B-HS/keyboard/dist/assets/1x1.5 R1-AGZeUWU5.stl

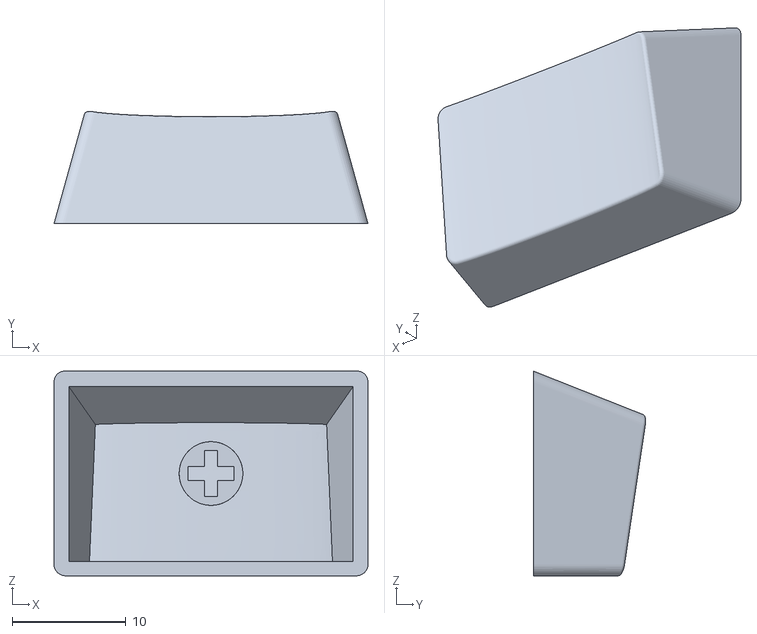
[picture p17: CAD file, 2026-04-19]
dist/assets/1x1.5 R1-AGZeUWU5.stl
27.6 x 9.86 x 18.0
