B-HS/keyboard/dist/assets/1x2 R3-Cc2chU7F.stl

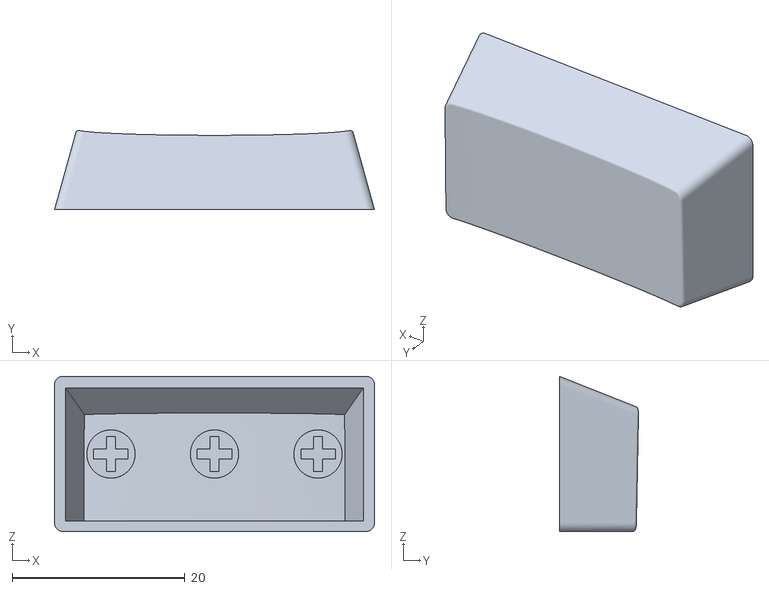
[picture p18: CAD file, 2026-04-19]
dist/assets/1x2 R3-Cc2chU7F.stl
37.1 x 9.17 x 18.0
