B-HS/keyboard/dist/assets/1x2 R2-B7yHtqF7.stl

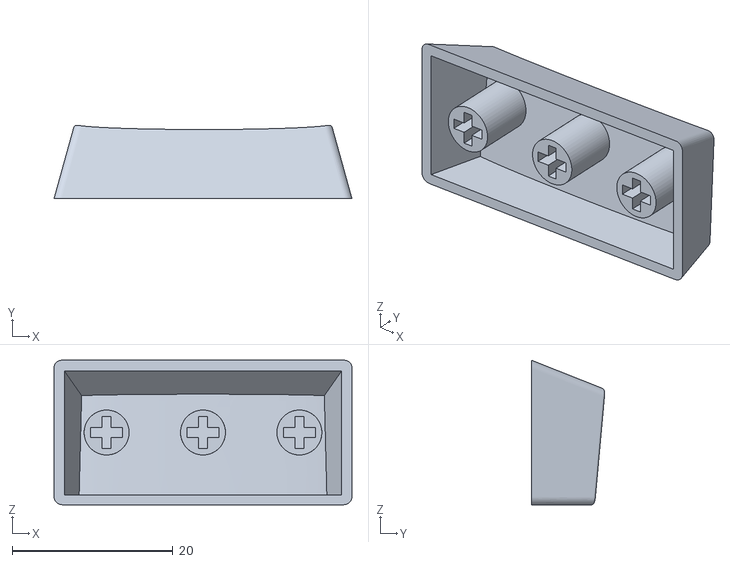
[picture p19: CAD file, 2026-04-19]
dist/assets/1x2 R2-B7yHtqF7.stl
37.1 x 9.12 x 18.0
