B-HS/keyboard/dist/assets/1x1.75 R2-CVJApBdu.stl

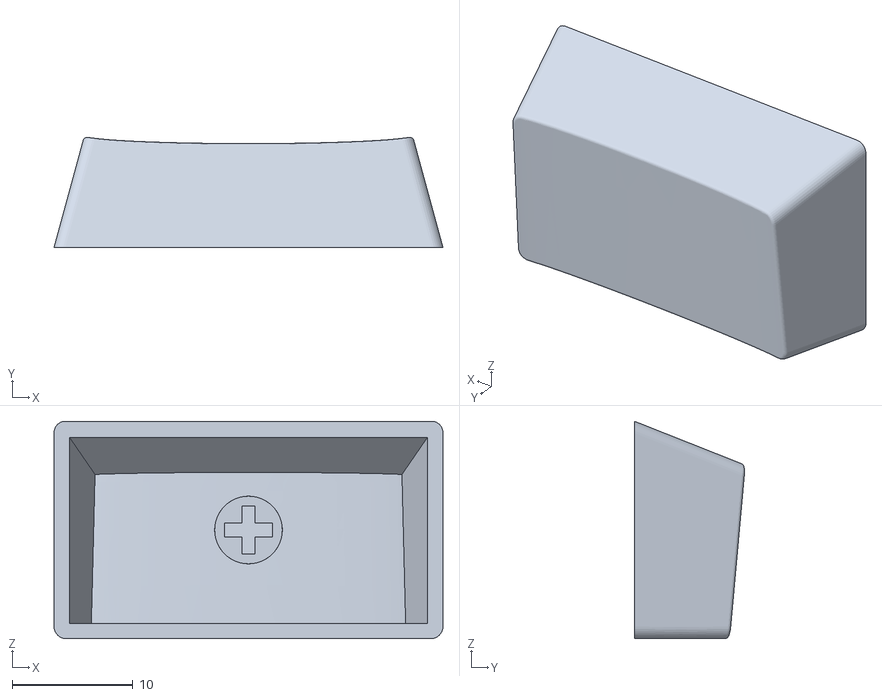
[picture p20: CAD file, 2026-04-19]
dist/assets/1x1.75 R2-CVJApBdu.stl
32.2 x 9.10 x 18.0
