B-HS/keyboard/dist/assets/1x1 R2-BPDmK7m8.stl

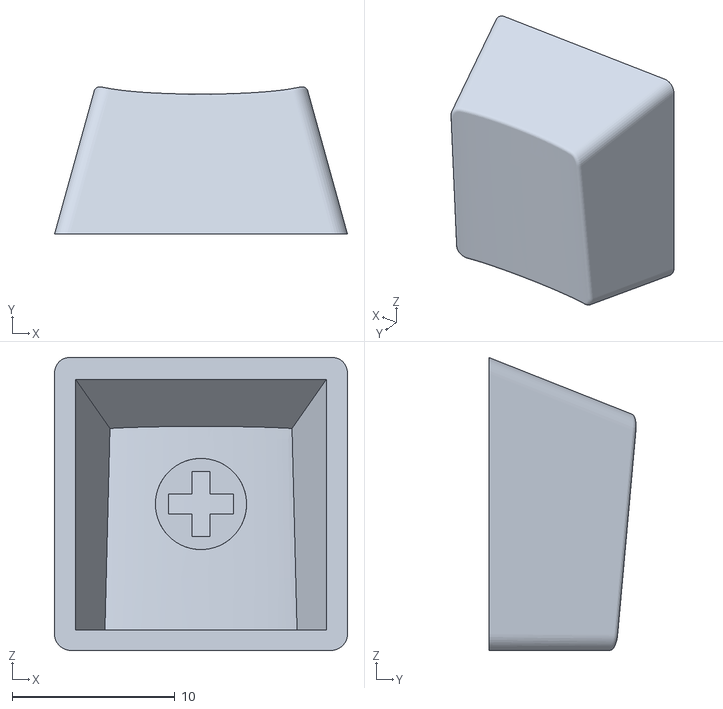
[picture p21: CAD file, 2026-04-19]
dist/assets/1x1 R2-BPDmK7m8.stl
18.0 x 9.04 x 18.0
