B-HS/keyboard/dist/assets/1x1.75 R4-D09ORx_c.stl

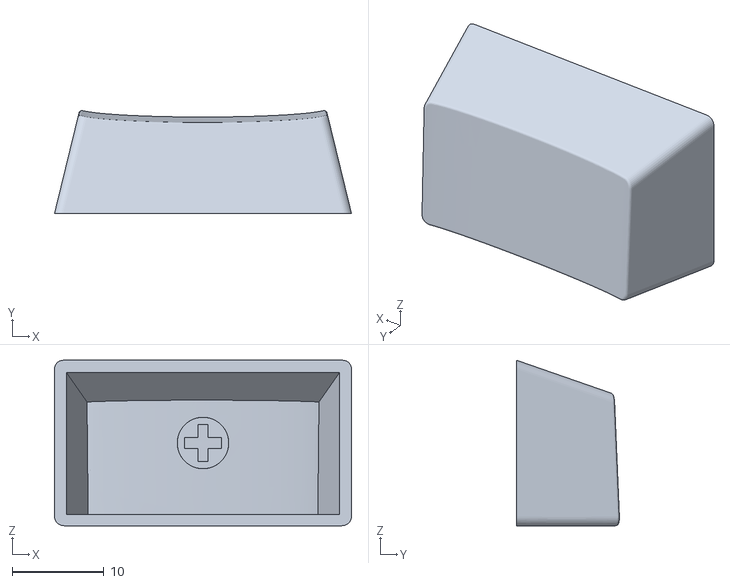
[picture p22: CAD file, 2026-04-19]
dist/assets/1x1.75 R4-D09ORx_c.stl
32.3 x 11.2 x 18.0
