B-HS/keyboard/dist/assets/1x1.75 R1-Bo90p1ow.stl

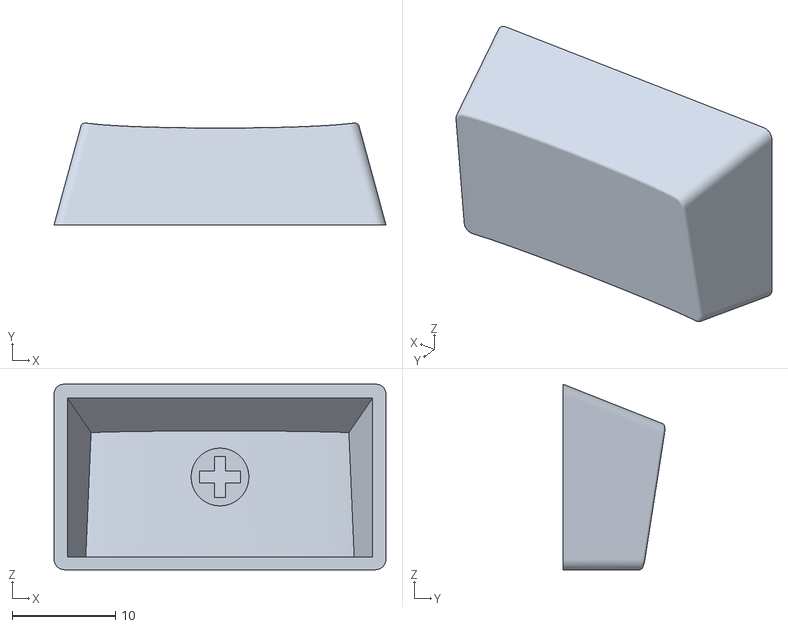
[picture p23: CAD file, 2026-04-19]
dist/assets/1x1.75 R1-Bo90p1ow.stl
32.2 x 9.87 x 18.0
