B-HS/keyboard/dist/assets/1x1.5 R2-BYpHddNk.stl

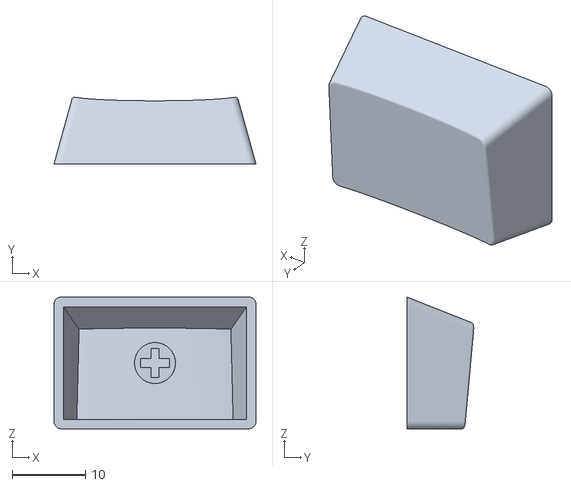
[picture p24: CAD file, 2026-04-19]
dist/assets/1x1.5 R2-BYpHddNk.stl
27.6 x 9.09 x 18.0
