B-HS/keyboard/dist/assets/1x2 R4-B8nouRfq.stl

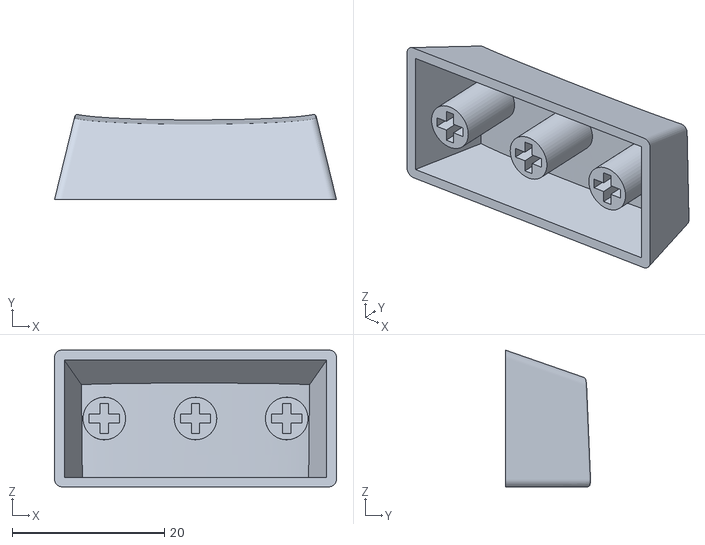
[picture p25: CAD file, 2026-04-19]
dist/assets/1x2 R4-B8nouRfq.stl
37.1 x 11.2 x 18.0
