B-HS/keyboard/dist/assets/1x1.5 R4-Dm8Txsvt.stl

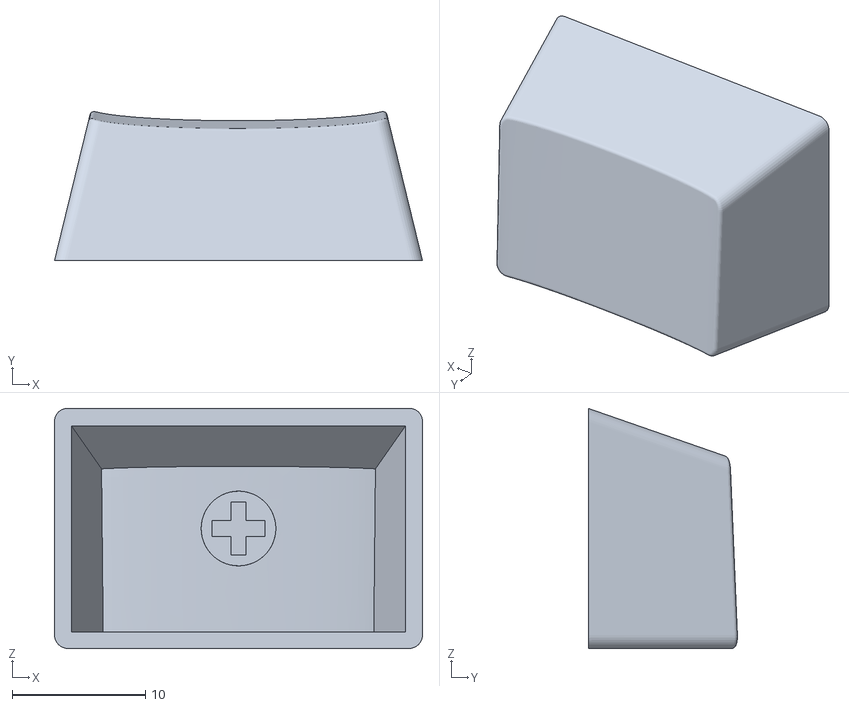
[picture p26: CAD file, 2026-04-19]
dist/assets/1x1.5 R4-Dm8Txsvt.stl
27.6 x 11.2 x 18.0
