B-HS/keyboard/dist/assets/1x1 R3-C7WHg33m.stl

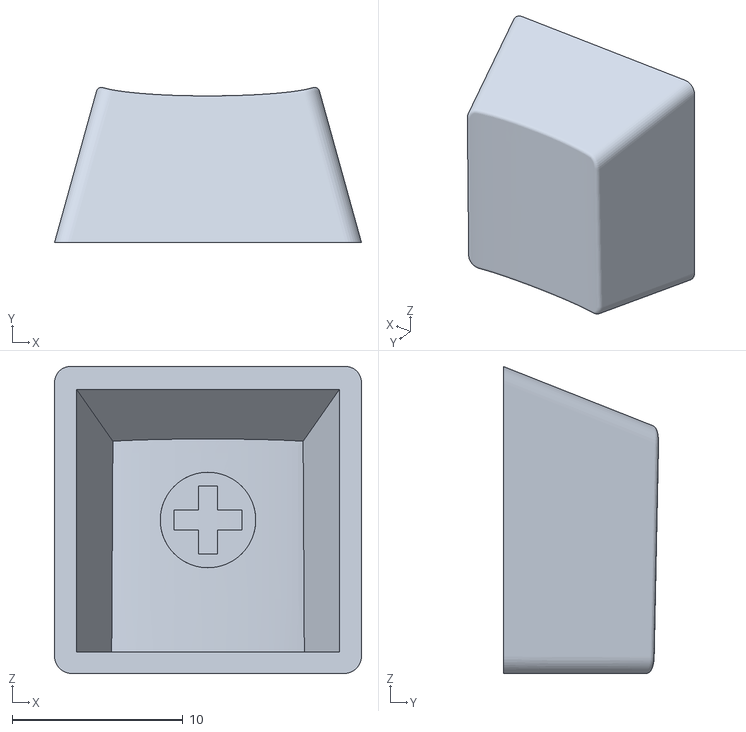
[picture p27: CAD file, 2026-04-19]
dist/assets/1x1 R3-C7WHg33m.stl
18.0 x 9.09 x 18.0
