B-HS/keyboard/dist/assets/1x1 R1-C5EL7BkD.stl

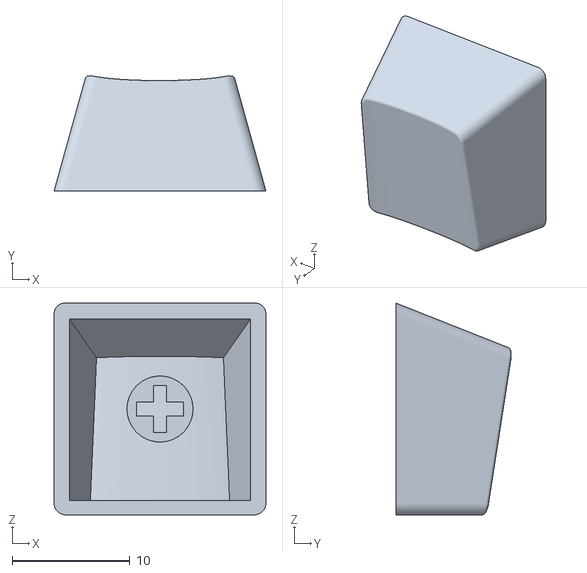
[picture p28: CAD file, 2026-04-19]
dist/assets/1x1 R1-C5EL7BkD.stl
18.0 x 9.80 x 18.0
