B-HS/keyboard/dist/assets/1x2 R1-t59L7Y_R.stl

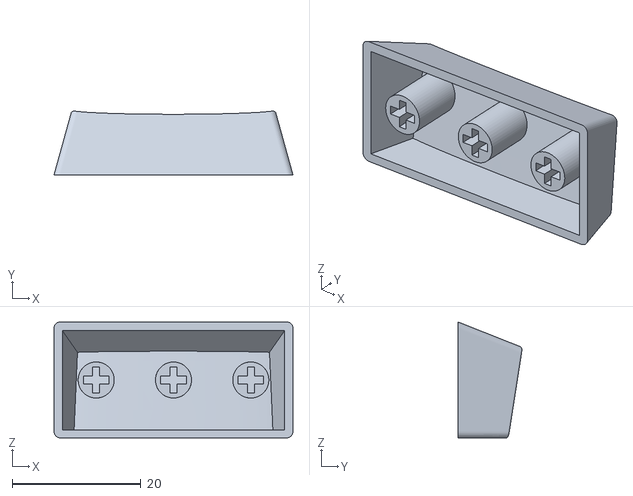
[picture p29: CAD file, 2026-04-19]
dist/assets/1x2 R1-t59L7Y_R.stl
37.1 x 9.88 x 18.0
