B-HS/keyboard/dist/assets/1x2.5 R3-bn9iJfxd.stl

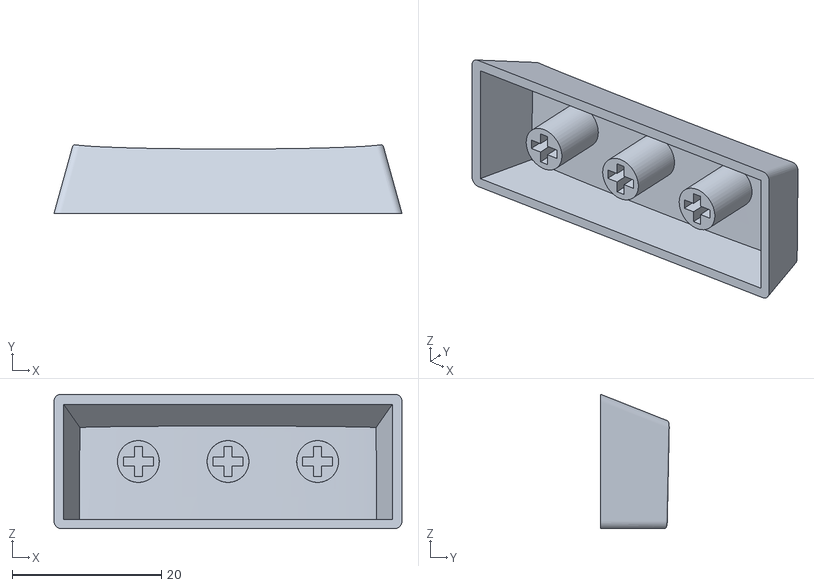
[picture p30: CAD file, 2026-04-19]
dist/assets/1x2.5 R3-bn9iJfxd.stl
46.6 x 9.18 x 18.0
