B-HS/keyboard/dist/assets/1x1.75 R3-BIYnu4hX.stl

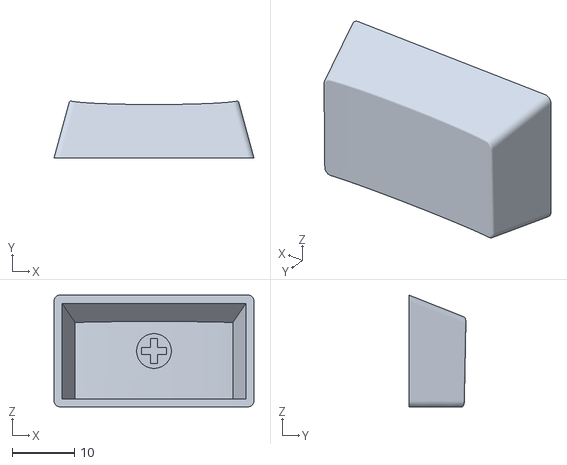
[picture p31: CAD file, 2026-04-19]
dist/assets/1x1.75 R3-BIYnu4hX.stl
32.2 x 9.15 x 18.0
