B-HS/keyboard/dist/assets/1x2.5 R1-ClbsR-en.stl

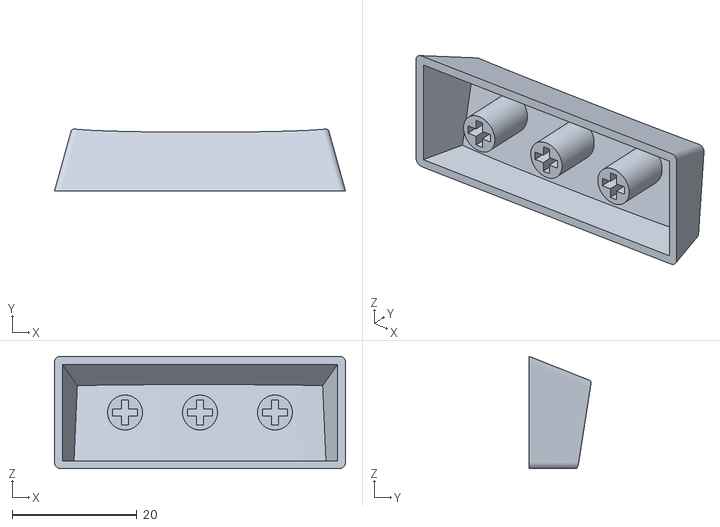
[picture p32: CAD file, 2026-04-19]
dist/assets/1x2.5 R1-ClbsR-en.stl
46.6 x 9.90 x 18.0
