B-HS/keyboard/dist/assets/1x2.5 R2-CQJdyVL4.stl

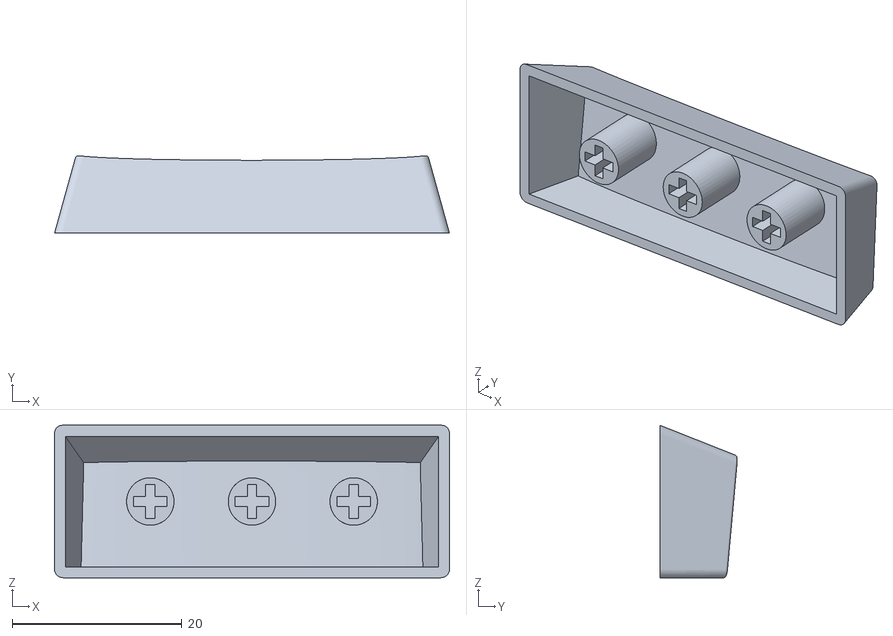
[picture p33: CAD file, 2026-04-19]
dist/assets/1x2.5 R2-CQJdyVL4.stl
46.6 x 9.13 x 18.0
