B-HS/keyboard/dist/assets/1x2.25 R3-CNCmQNf8.stl

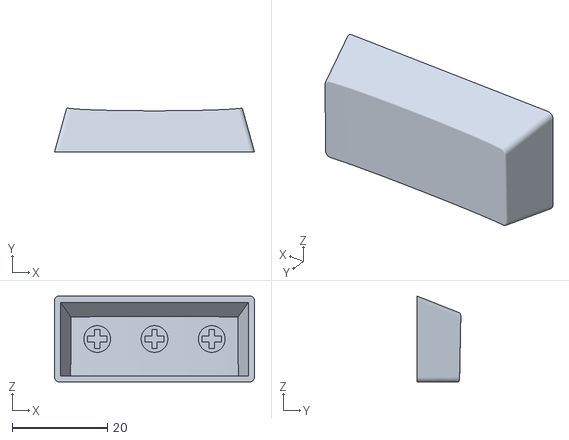
[picture p34: CAD file, 2026-04-19]
dist/assets/1x2.25 R3-CNCmQNf8.stl
41.9 x 9.16 x 18.0
