B-HS/keyboard/dist/assets/1x2.25 R2-BCx2EO4n.stl

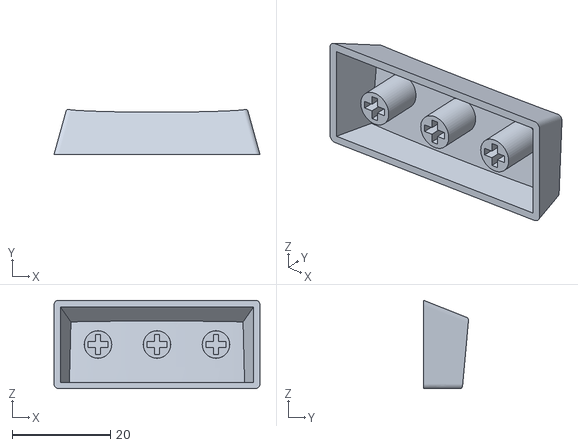
[picture p35: CAD file, 2026-04-19]
dist/assets/1x2.25 R2-BCx2EO4n.stl
41.9 x 9.12 x 18.0
