B-HS/keyboard/dist/assets/1x6.25 R4-NUg3-Npx.stl

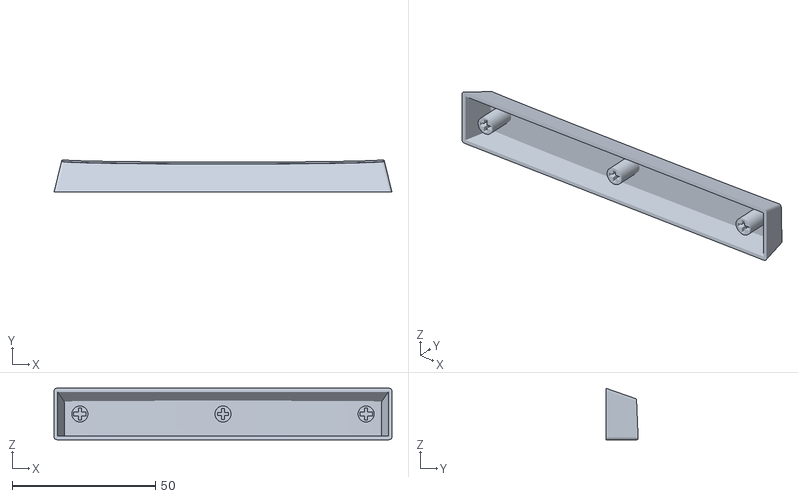
[picture p36: CAD file, 2026-04-19]
dist/assets/1x6.25 R4-NUg3-Npx.stl
118.1 x 11.3 x 18.0
