B-HS/keyboard/dist/assets/1x2.5 R4-DDGQGMGy.stl

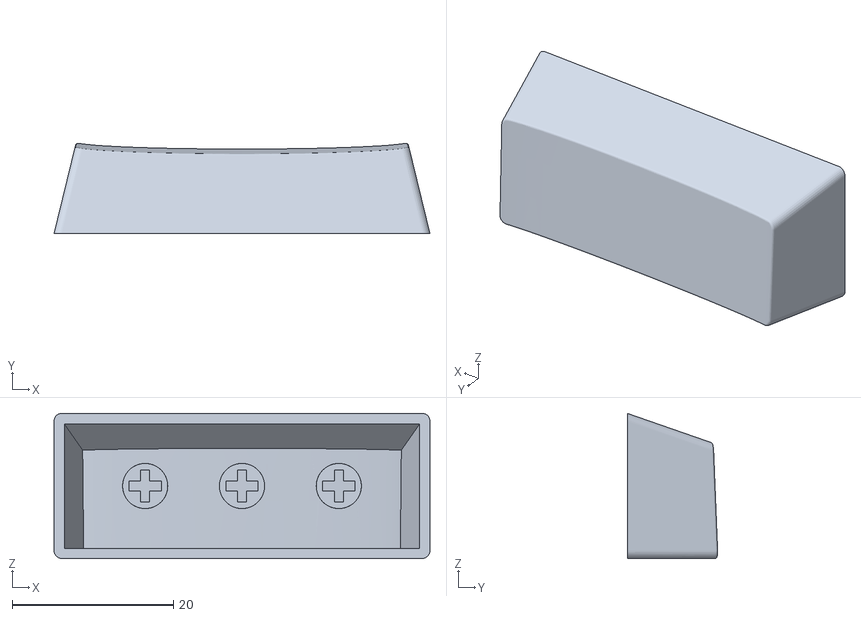
[picture p37: CAD file, 2026-04-19]
dist/assets/1x2.5 R4-DDGQGMGy.stl
46.6 x 11.2 x 18.0
