B-HS/keyboard/dist/assets/1x2.25 R4-CDf46tqj.stl

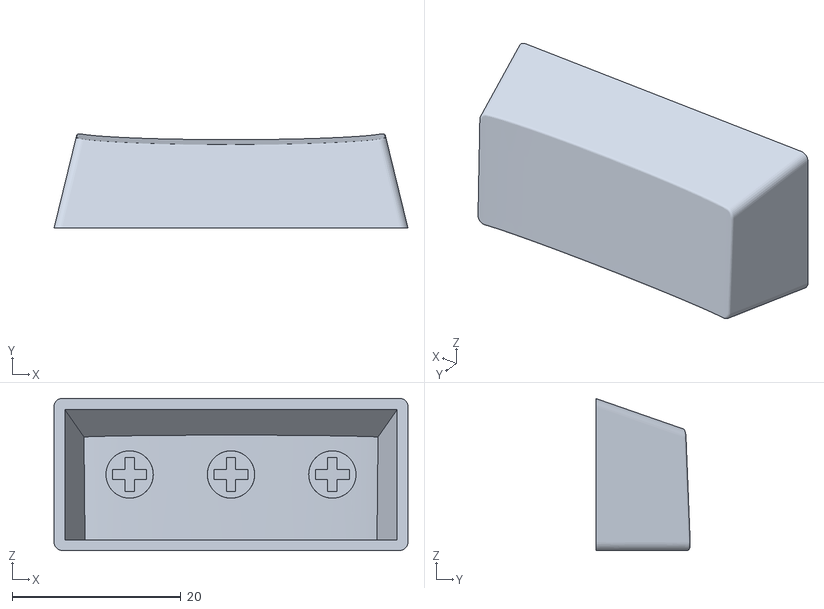
[picture p38: CAD file, 2026-04-19]
dist/assets/1x2.25 R4-CDf46tqj.stl
41.9 x 11.2 x 18.0
