B-HS/keyboard/dist/assets/1x6.25 R2-C1Yu1_Mv.stl

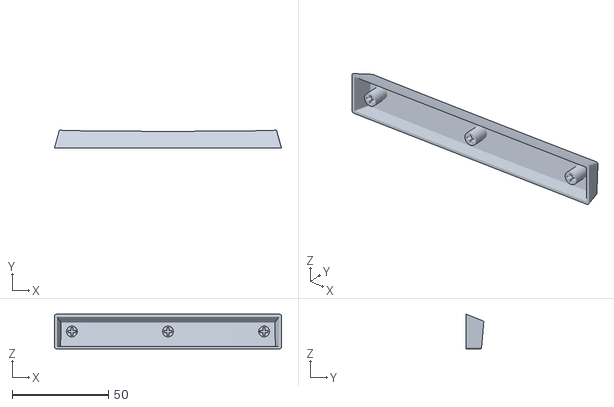
[picture p39: CAD file, 2026-04-19]
dist/assets/1x6.25 R2-C1Yu1_Mv.stl
118.1 x 9.18 x 18.0
