B-HS/keyboard/dist/assets/1x6.25 R1-CkT0OtEM.stl

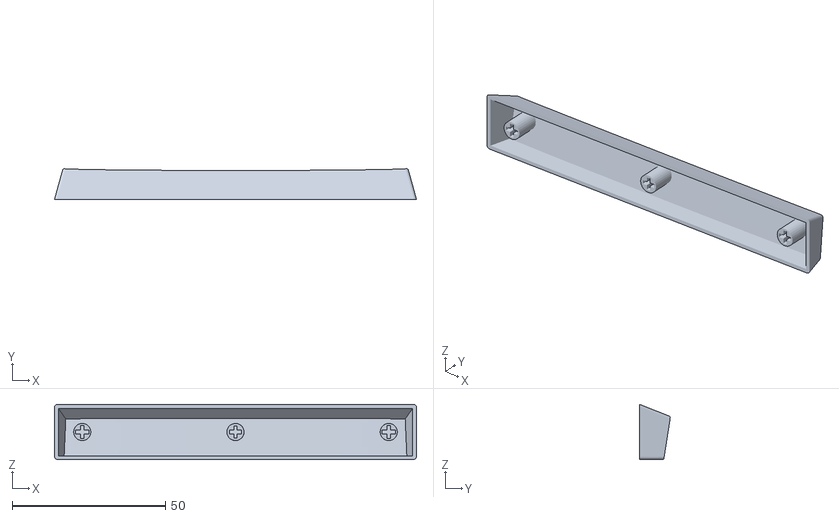
[picture p40: CAD file, 2026-04-19]
dist/assets/1x6.25 R1-CkT0OtEM.stl
118.1 x 9.96 x 18.0
