B-HS/keyboard/dist/assets/1x1.25 R1-BTIr3D3i.stl

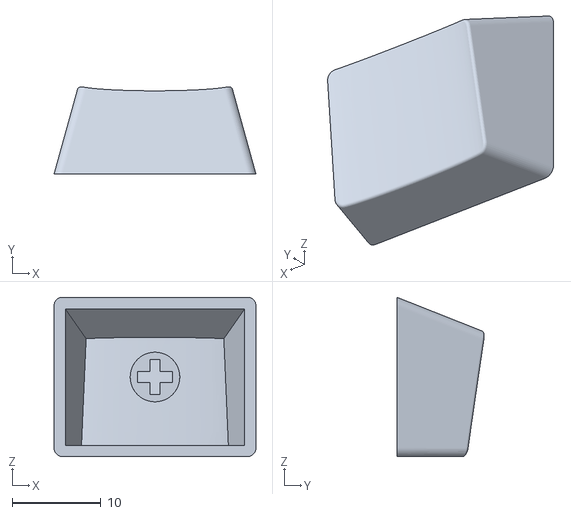
[picture p41: CAD file, 2026-04-19]
dist/assets/1x1.25 R1-BTIr3D3i.stl
22.8 x 9.84 x 18.0
