B-HS/keyboard/dist/assets/1x2.25 R1-BjnI8IJX.stl

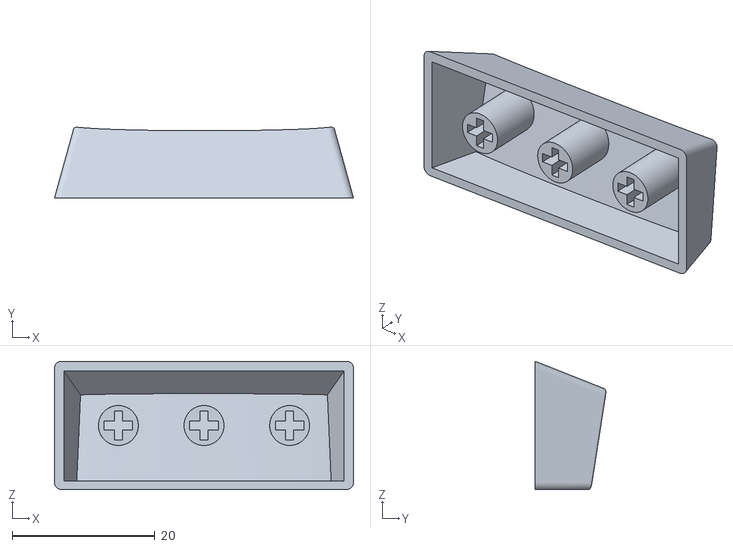
[picture p42: CAD file, 2026-04-19]
dist/assets/1x2.25 R1-BjnI8IJX.stl
41.9 x 9.89 x 18.0
